sylvainbruand/FLAQ-FabLab-Air-Quality/flaq_xiao/FLAQ-3.png

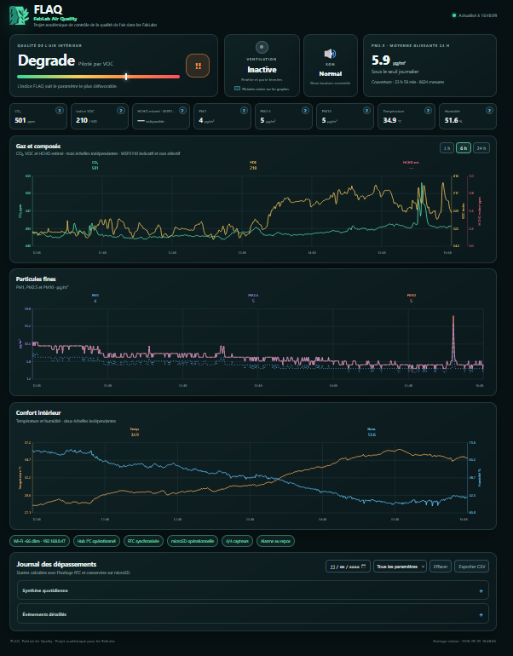
flaq_xiao/FLAQ-3.png
