sylvainbruand/FLAQ-FabLab-Air-Quality/flaq_xiao/SW/2-102010671-seeedstudio-xiao-esp32s3-plus-45font.jpg

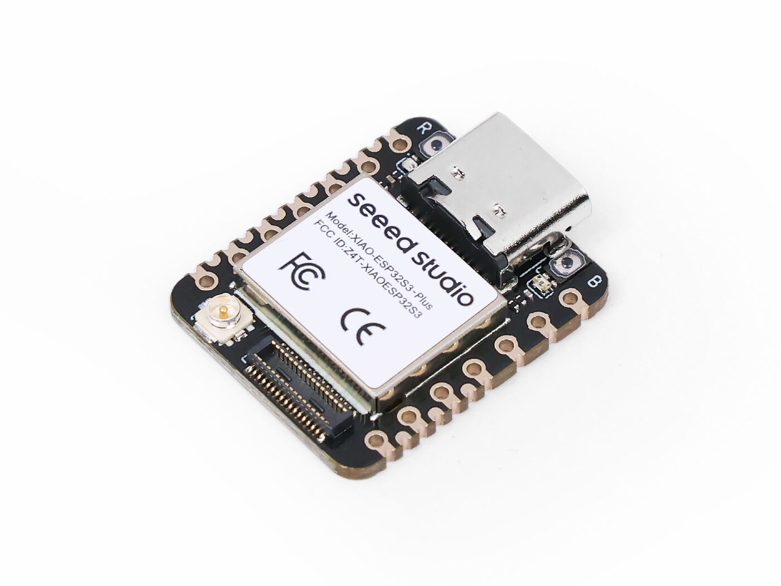
flaq_xiao/SW/2-102010671-seeedstudio-xiao-esp32s3-plus-45font.jpg
