sylvainbruand/FLAQ-FabLab-Air-Quality/flaq_xiao/SW/aeraulique-ventilation-gris.jpg

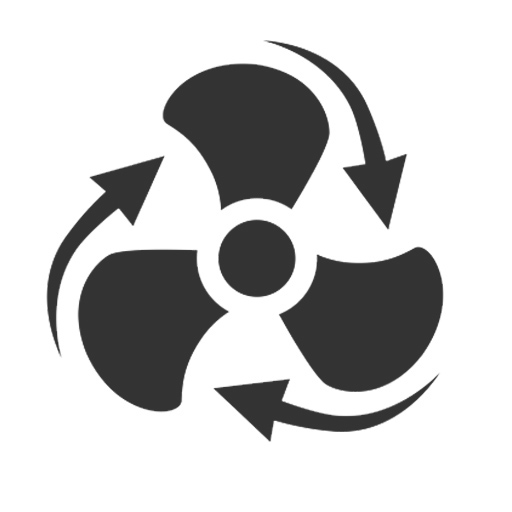
flaq_xiao/SW/aeraulique-ventilation-gris.jpg
