sylvainbruand/FLAQ-FabLab-Air-Quality/flaq_xiao/SW/modeles_3d/grove_8_ports/dessus.jpg

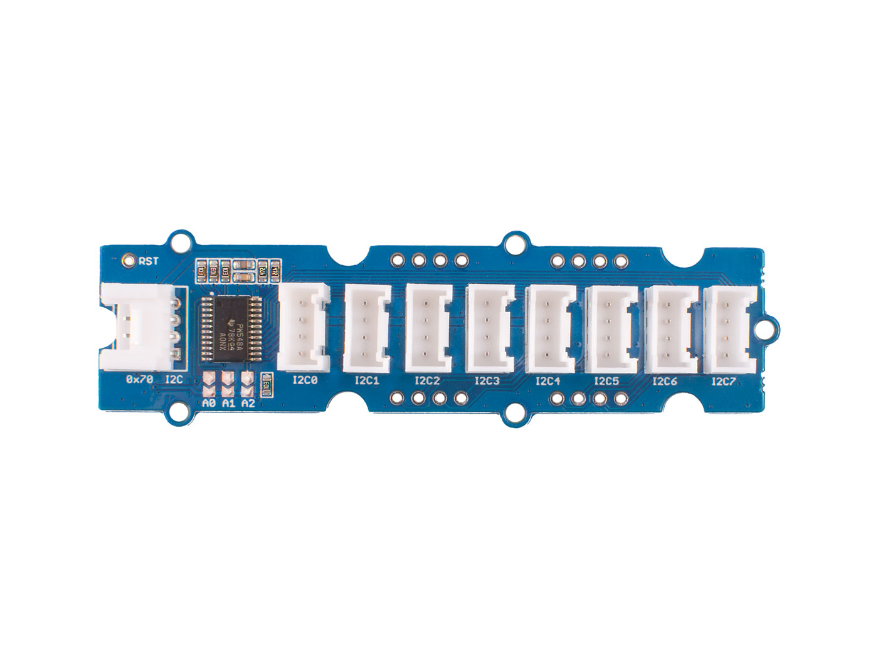
flaq_xiao/SW/modeles_3d/grove_8_ports/dessus.jpg
