sylvainbruand/FLAQ-FabLab-Air-Quality/flaq_xiao/SW/modeles_3d/scd30/apercu.bmp

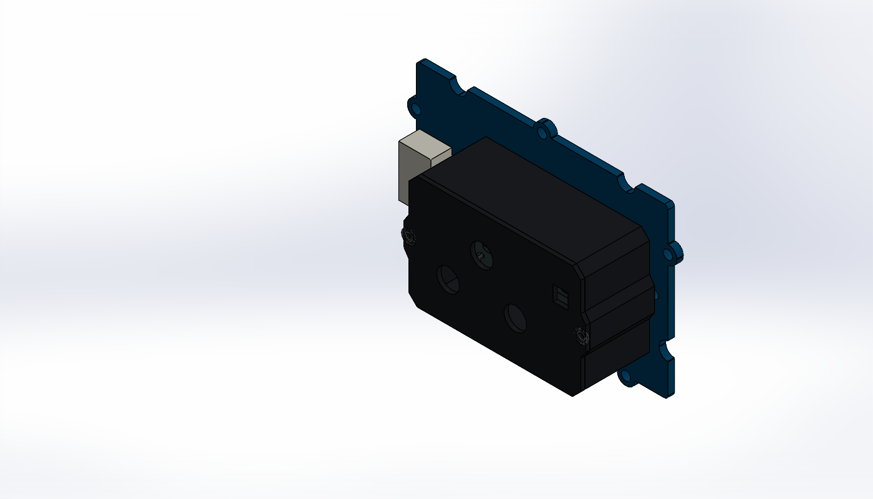
flaq_xiao/SW/modeles_3d/scd30/apercu.bmp
