sylvainbruand/FLAQ-FabLab-Air-Quality/flaq_xiao/SW/modeles_3d/scd30/import.bmp

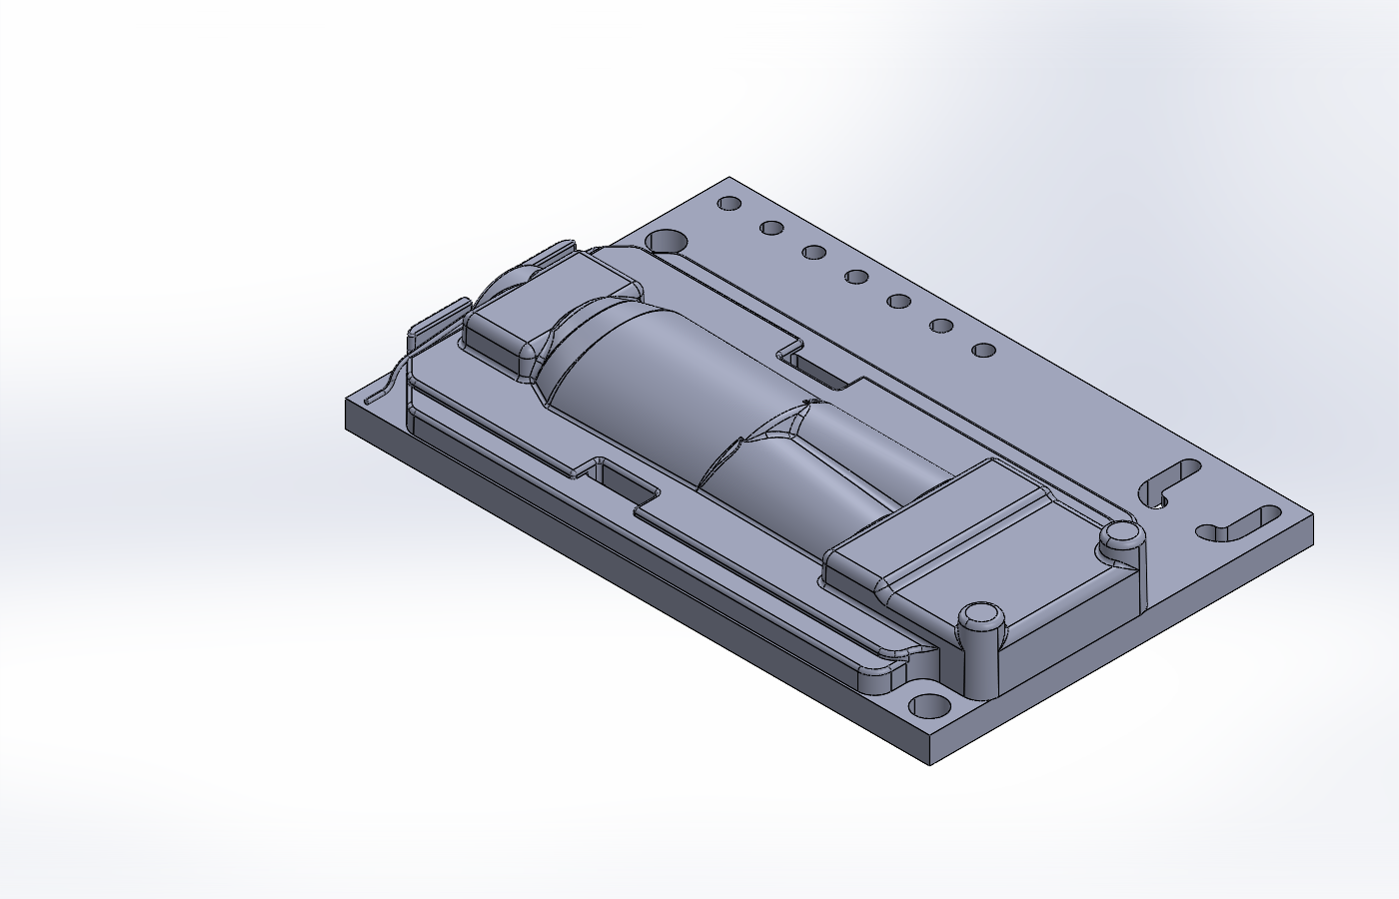
flaq_xiao/SW/modeles_3d/scd30/import.bmp
