sylvainbruand/FLAQ-FabLab-Air-Quality/flaq_xiao/SW/Screenshot 2025-02-27 170238.png

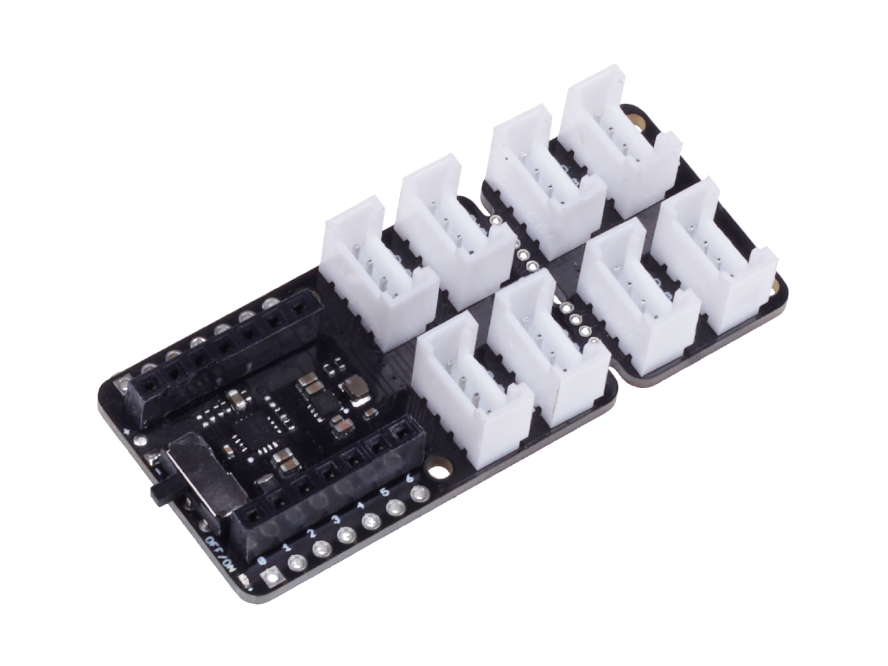
flaq_xiao/SW/Screenshot 2025-02-27 170238.png
