sylvainbruand/FLAQ-FabLab-Air-Quality/flaq_xiao/SW/OLED 128x64.SLDPRT

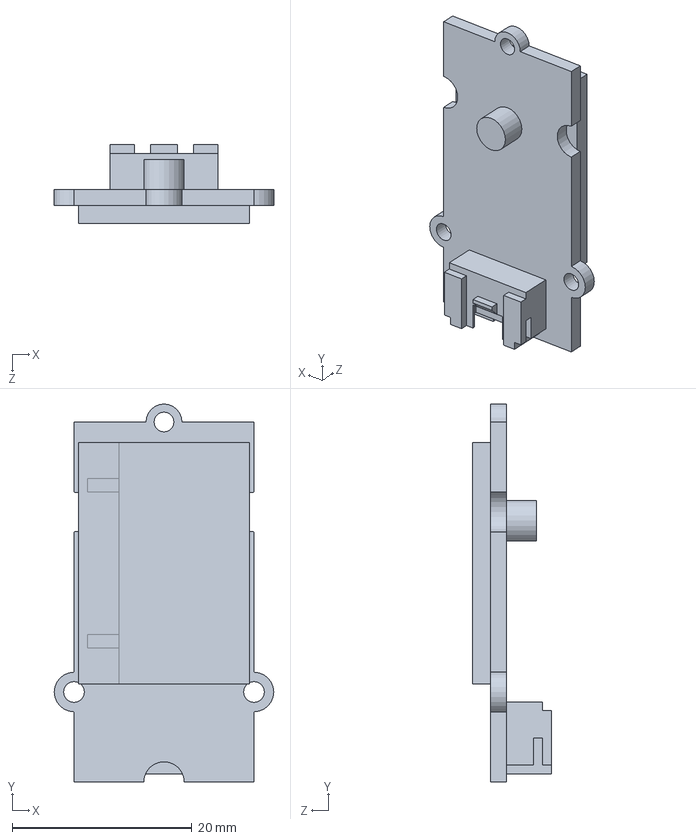
[picture p19: CAD file, 2026-09-29]
flaq_xiao/SW/OLED 128x64.SLDPRT
24.4 x 42.0 x 8.81 mm
