sylvainbruand/FLAQ-FabLab-Air-Quality/flaq_xiao/SW/Grove Shield for Seeeduino XIAO v1.step

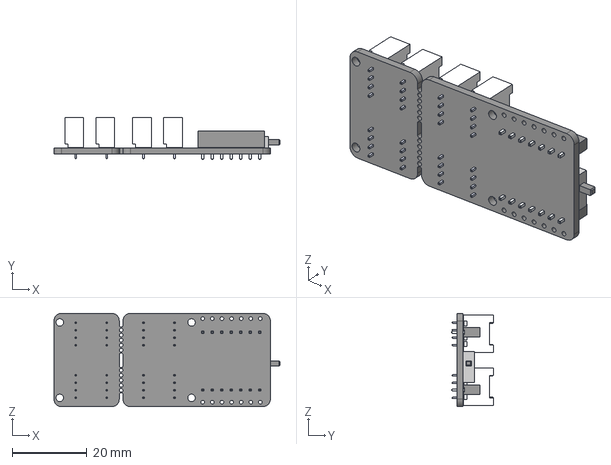
[picture p20: CAD file, 2026-09-29]
flaq_xiao/SW/Grove Shield for Seeeduino XIAO v1.step
60.4 x 11.2 x 24.9 mm
Grove Connector (standing) x 8
FemaleHeader x 2
