sylvainbruand/FLAQ-FabLab-Air-Quality/flaq_xiao/SW/buzzer.SLDPRT

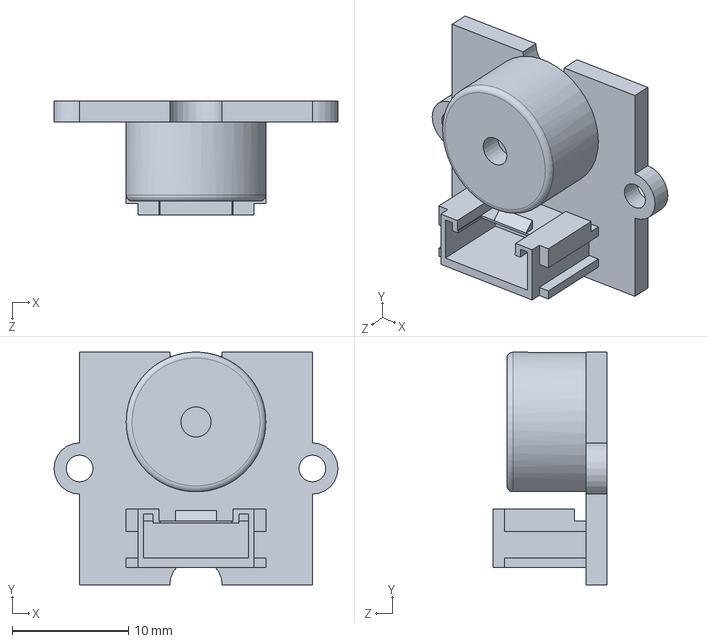
[picture p21: CAD file, 2026-09-29]
flaq_xiao/SW/buzzer.SLDPRT
24.4 x 20.0 x 9.80 mm
