sylvainbruand/FLAQ-FabLab-Air-Quality/flaq_xiao/SW/toit_xiao_V2.SLDPRT

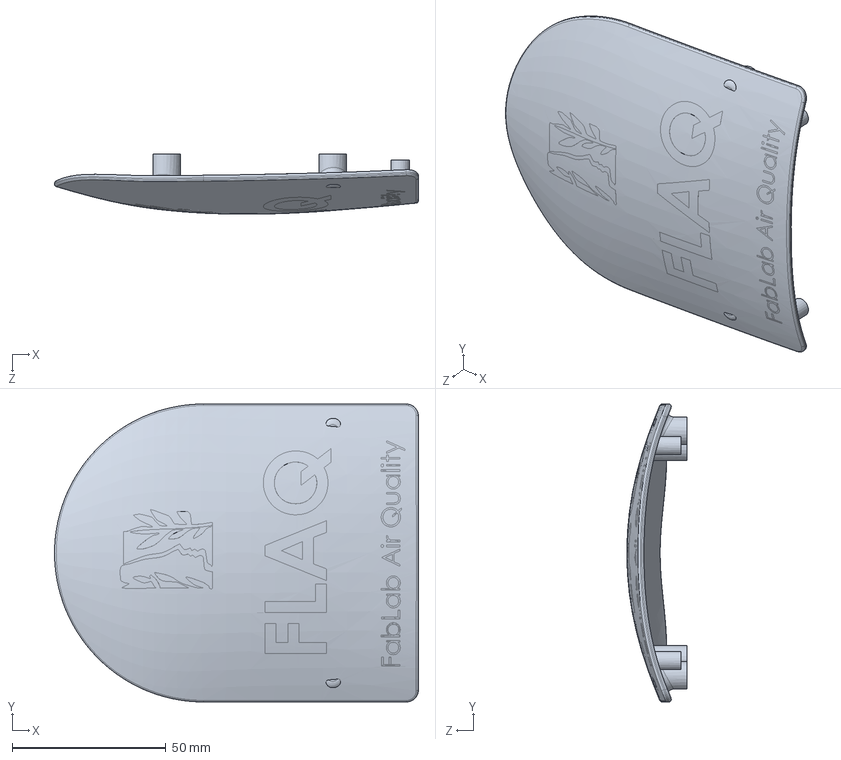
[picture p22: CAD file, 2026-09-29]
flaq_xiao/SW/toit_xiao_V2.SLDPRT
118.5 x 97.0 x 19.7 mm
