sylvainbruand/FLAQ-FabLab-Air-Quality/flaq_xiao/SW/XIAO ESP32S3 PLUS v4.step

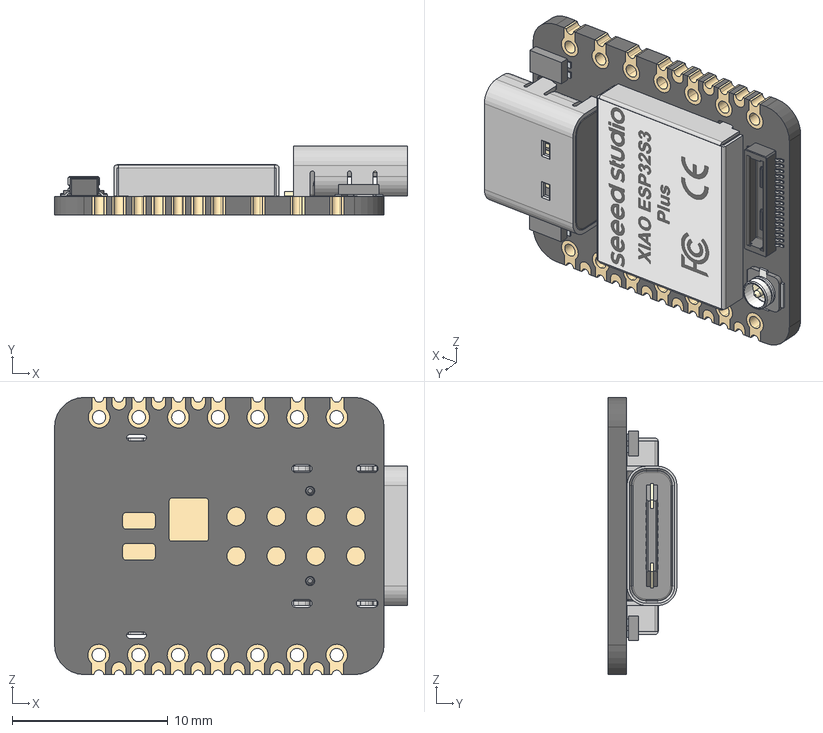
[picture p23: CAD file, 2026-09-29]
flaq_xiao/SW/XIAO ESP32S3 PLUS v4.step
22.6 x 4.42 x 17.8 mm
DF40C-30DP-0.4V_51_ v1
BOSS-EXTRUDE14_8_
BOSS-EXTRUDE7_4_
BOSS-EXTRUDE7_3_
BOSS-EXTRUDE14_4_
BOSS-EXTRUDE14_2_
BOSS-EXTRUDE14_11_
BOSS-EXTRUDE7_7_
BOSS-EXTRUDE14_9_
BOSS-EXTRUDE14_3_
BOSS-EXTRUDE14_7_
MIRROR2
BOSS-EXTRUDE14_5_
BOSS-EXTRUDE14_12_
BOSS-EXTRUDE7_8_
BOSS-EXTRUDE7_1_
BOSS-EXTRUDE14_10_
BOSS-EXTRUDE7_9_
BOSS-EXTRUDE14_6_
BOSS-EXTRUDE14_1_
BOSS-EXTRUDE7_6_
BOSS-EXTRUDE7_2_
CUT-EXTRUDE5
BOSS-EXTRUDE7_5_
Shield
Pins x 2
U.FL-R-SMT-1_10_ v1
