sylvainbruand/FLAQ-FabLab-Air-Quality/flaq_xiao/SW/T°C Humidité.SLDPRT

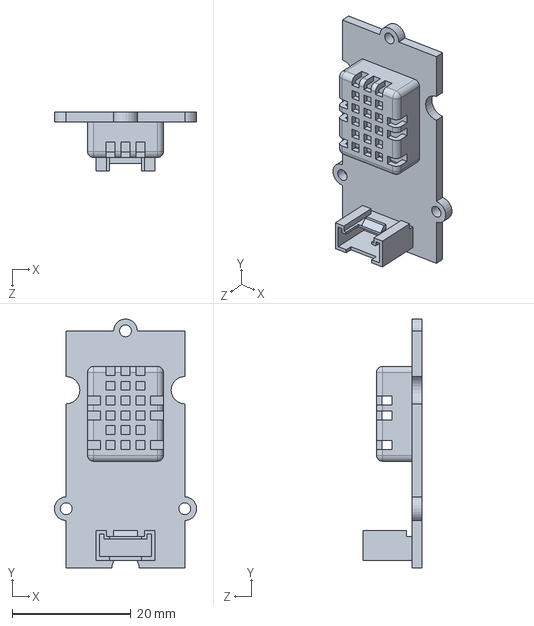
[picture p24: CAD file, 2026-09-29]
flaq_xiao/SW/T°C Humidité.SLDPRT
24.0 x 42.0 x 10.0 mm
