sylvainbruand/FLAQ-FabLab-Air-Quality/flaq_xiao/SW/couvercle_xiao-1.3mf

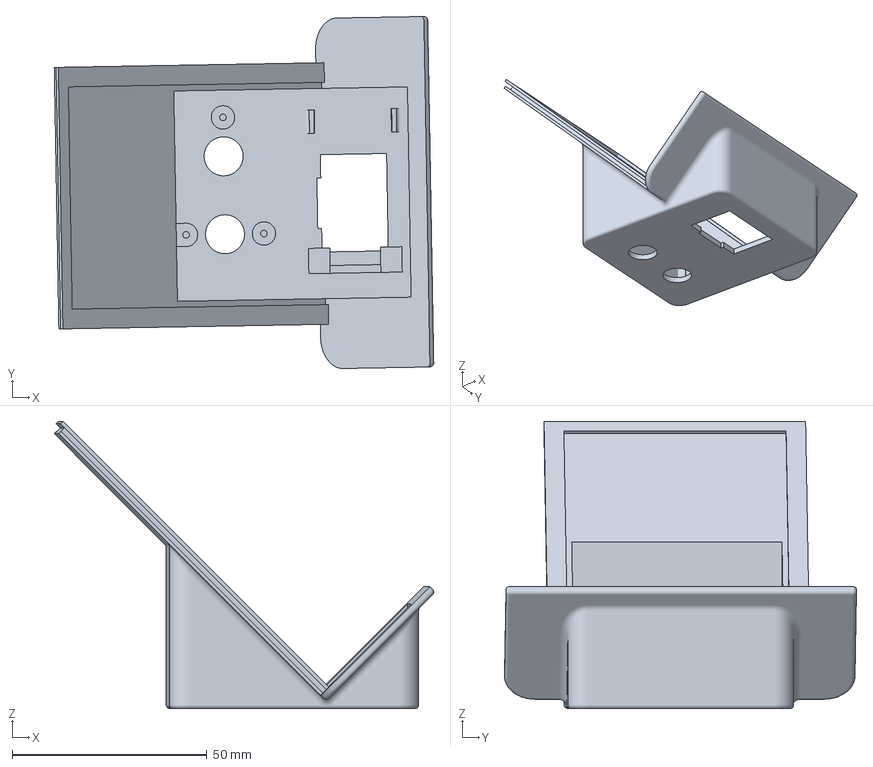
[picture p25: CAD file, 2026-09-04]
flaq_xiao/SW/couvercle_xiao-1.3mf
97.4 x 90.4 x 73.8 mm
