sylvainbruand/FLAQ-FabLab-Air-Quality/flaq_xiao/SW/couvercle_xiao.SLDPRT

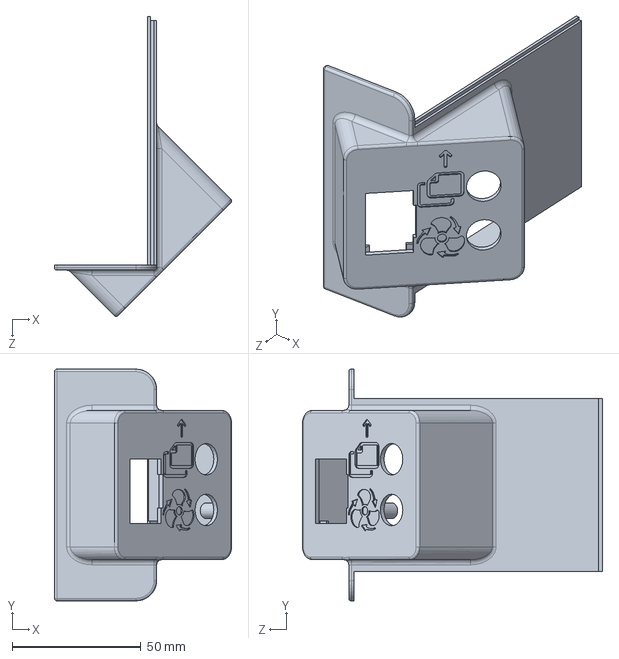
[picture p26: CAD file, 2026-09-04]
flaq_xiao/SW/couvercle_xiao.SLDPRT
68.8 x 90.0 x 116.5 mm
