sylvainbruand/FLAQ-FabLab-Air-Quality/flaq_xiao/SW/logo_BP_xiao.SLDPRT

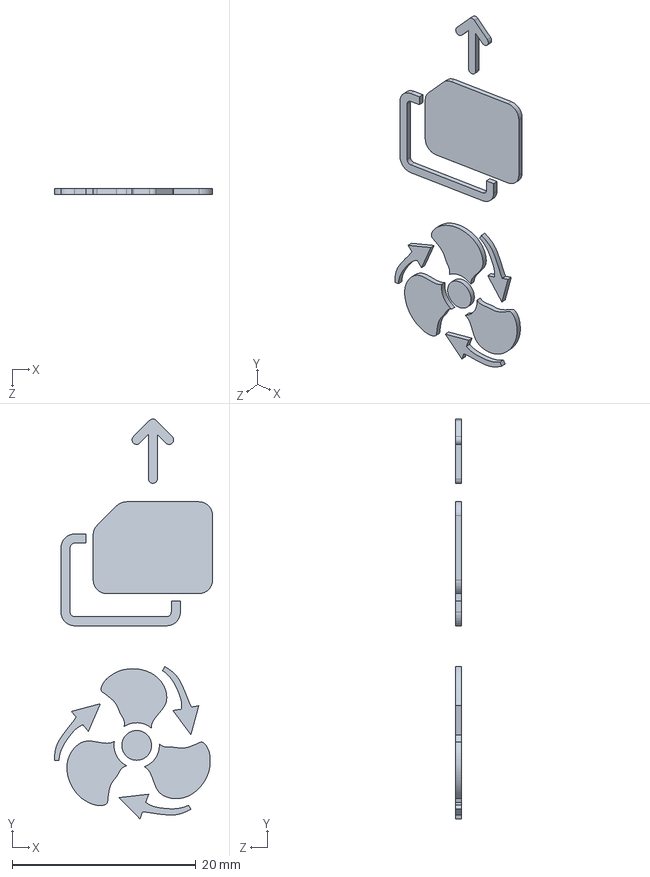
[picture p27: CAD file, 2026-09-04]
flaq_xiao/SW/logo_BP_xiao.SLDPRT
17.2 x 43.5 x 0.6 mm
