sylvainbruand/FLAQ-FabLab-Air-Quality/flaq_xiao/SW/bouchon_droite.SLDPRT

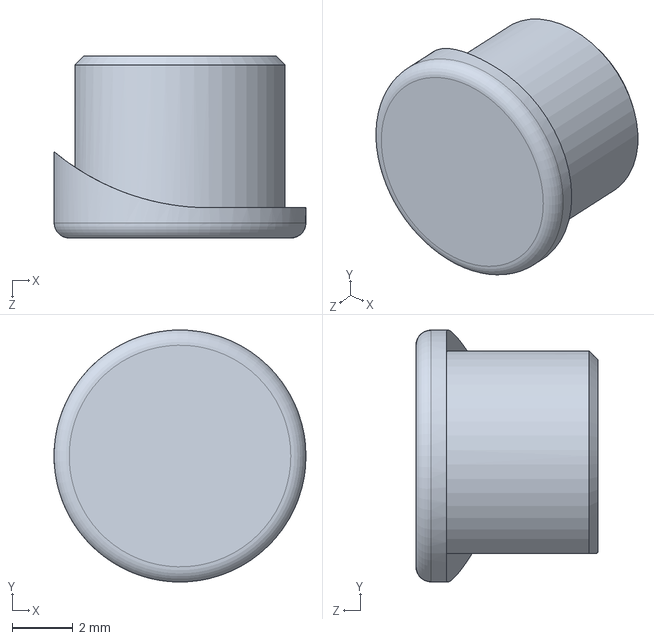
[picture p28: CAD file, 2026-08-22]
flaq_xiao/SW/bouchon_droite.SLDPRT
8.30 x 8.30 x 6.00 mm
