sylvainbruand/FLAQ-FabLab-Air-Quality/flaq_xiao/SW/bouchon2.SLDPRT

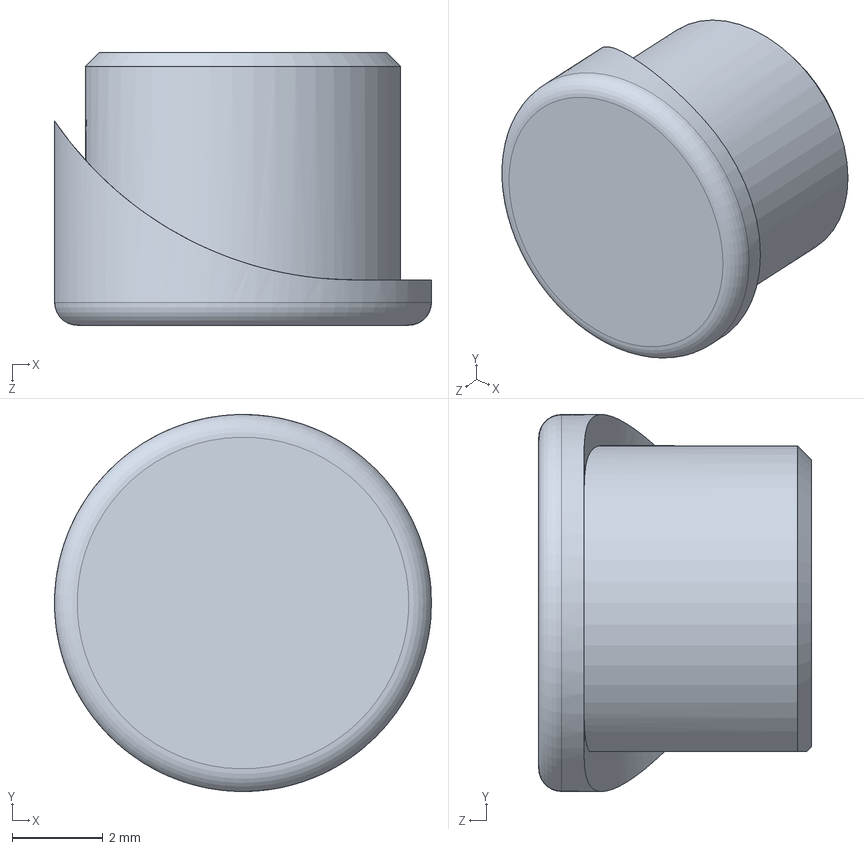
[picture p29: CAD file, 2026-08-22]
flaq_xiao/SW/bouchon2.SLDPRT
8.30 x 8.30 x 6.00 mm
