sylvainbruand/FLAQ-FabLab-Air-Quality/flaq_xiao/SW/etage stevenson.SLDPRT

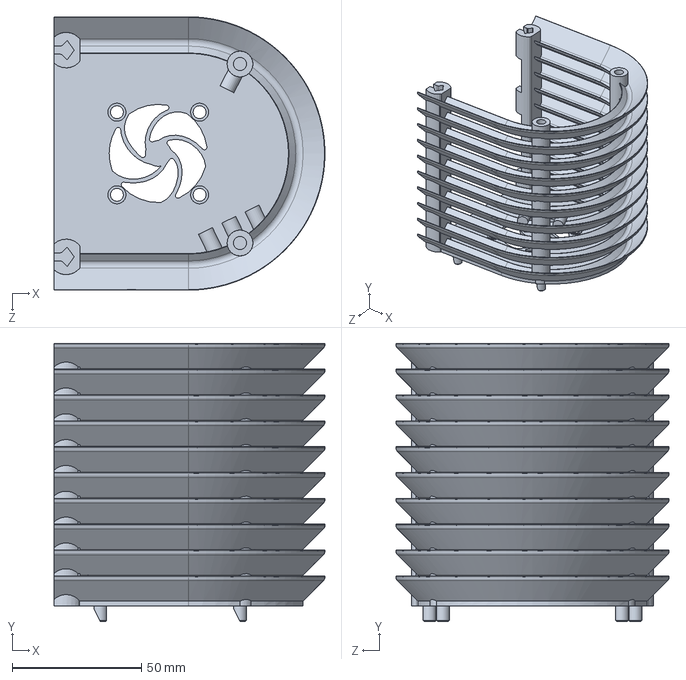
[picture p30: CAD file, 2026-08-22]
flaq_xiao/SW/etage stevenson.SLDPRT
104.9 x 107.8 x 105.8 mm
