sylvainbruand/FLAQ-FabLab-Air-Quality/flaq_xiao/SW/boitier bas.SLDPRT

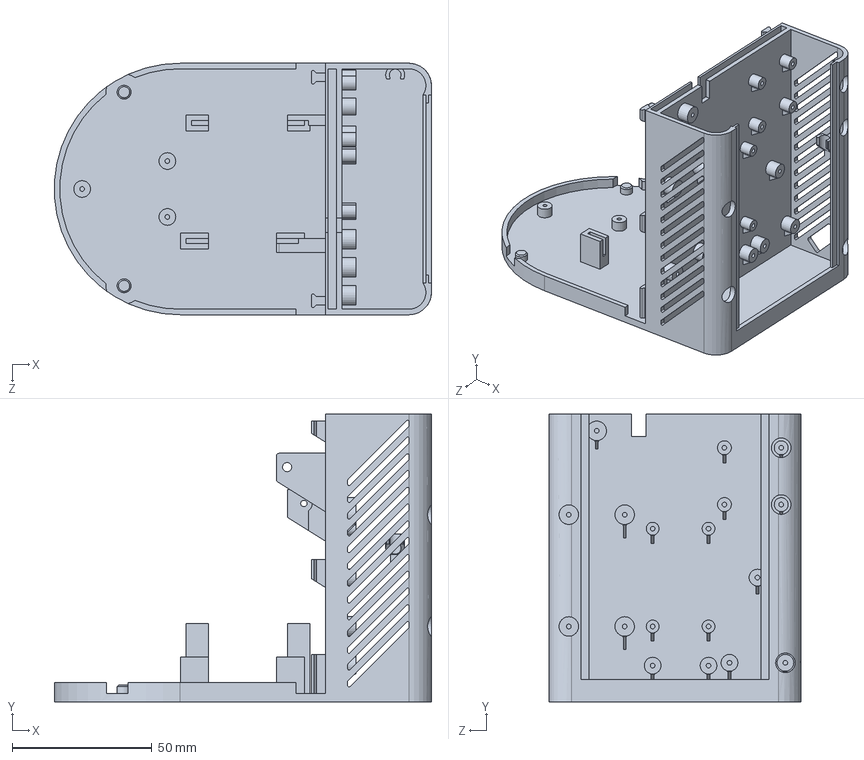
[picture p31: CAD file, 2026-08-22]
flaq_xiao/SW/boitier bas.SLDPRT
134.9 x 103.0 x 90.0 mm
