sylvainbruand/FLAQ-FabLab-Air-Quality/flaq_xiao/SW/flaq-xiao.3mf

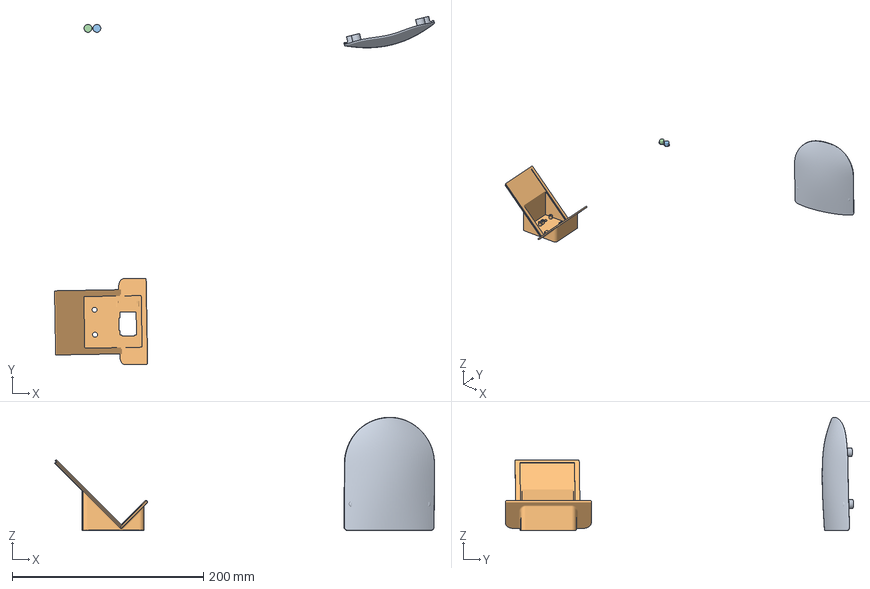
[picture p32: CAD file, 2026-08-22]
flaq_xiao/SW/flaq-xiao.3mf
397.3 x 364.3 x 118.5 mm
toit_xiao
Assemblage1^ensemble_xiao - couvercle_xiao-1
bouchon_droite.STL x 2
