sylvainbruand/FLAQ-FabLab-Air-Quality/flaq_xiao/flaq_logo.h

#pragma once

#include <Arduino.h>

const uint8_t FLAQ_LOGO_PNG[] PROGMEM = {
    0x89, 0x50, 0x4e, 0x47, 0x0d, 0x0a, 0x1a, 0x0a, 0x00, 0x00, 0x00, 0x0d,
    0x49, 0x48, 0x44, 0x52, 0x00, 0x00, 0x00, 0xc0, 0x00, 0x00, 0x00, 0xb6,
    0x08, 0x06, 0x00, 0x00, 0x00, 0x8f, 0xa7, 0x82, 0xdb, 0x00, 0x00, 0x00,
    0x01, 0x73, 0x52, 0x47, 0x42, 0x00, 0xae, 0xce, 0x1c, 0xe9, 0x00, 0x00,
    0x00, 0x04, 0x67, 0x41, 0x4d, 0x41, 0x00, 0x00, 0xb1, 0x8f, 0x0b, 0xfc,
    0x61, 0x05, 0x00, 0x00, 0x00, 0x09, 0x70, 0x48, 0x59, 0x73, 0x00, 0x00,
    0x0e, 0xc3, 0x00, 0x00, 0x0e, 0xc3, 0x01, 0xc7, 0x6f, 0xa8, 0x64, 0x00,
    0x00, 0x87, 0x91, 0x49, 0x44, 0x41, 0x54, 0x78, 0x5e, 0xed, 0xbd, 0x07,
    0x78, 0x56, 0xc7, 0x95, 0x37, 0x9e, 0x6f, 0xbf, 0x96, 0xdd, 0xec, 0x7e,
    0x9b, 0xdd, 0x6c, 0xb6, 0x17, 0x63, 0xc0, 0xc6, 0x80, 0x71, 0x2f, 0x49,
    0xdc, 0xed, 0xc4, 0x8e, 0x0b, 0x20, 0x09, 0x81, 0x3a, 0xc5, 0x14, 0x03,
    0xee, 0xf4, 0x22, 0x24, 0xd1, 0x9b, 0x40, 0xa8, 0x0b, 0x24, 0x8a, 0xc1,
    0x34, 0x21, 0xd4, 0xbb, 0x40, 0xd8, 0xd8, 0xc4, 0x76, 0x88, 0xed, 0x24,
    0x8e, 0x93, 0x0d, 0xa0, 0x57, 0x6f, 0x91, 0x5e, 0x75, 0x09, 0xb0, 0x1d,
    0x57, 0xcd, 0xff, 0x39, 0x33, 0x73, 0x66, 0xce, 0xcc, 0xbd, 0xaf, 0x10,
    0xd8, 0x9b, 0x75, 0xf2, 0xcf, 0x3c, 0xcf, 0x79, 0xee, 0x7d, 0xef, 0x9d,
    0x3b, 0x33, 0xf7, 0xbd, 0xbf, 0xdf, 0x99, 0x33, 0xed, 0xcc, 0x37, 0x22,
    0x77, 0x6f, 0x99, 0x38, 0x26, 0x3b, 0xb9, 0xf3, 0xb6, 0x9d, 0x6b, 0xbb,
    0xc7, 0xed, 0xdb, 0x96, 0xf6, 0x8d, 0xcb, 0x0c, 0x3e, 0x9f, 0xef, 0xcf,
    0x27, 0x14, 0x15, 0x84, 0x45, 0x17, 0xe5, 0xcd, 0x4a, 0x38, 0x98, 0x37,
    0x6b, 0x4a, 0xd1, 0x8e, 0x59, 0xdf, 0xdb, 0xbe, 0xf6, 0xf1, 0x5b, 0xf3,
    0x56, 0xff, 0x18, 0xce, 0xef, 0xda, 0xbe, 0xf6, 0xf1, 0x07, 0x77, 0x6e,
    0x1c, 0x17, 0xfd, 0x72, 0xd6, 0xd4, 0x87, 0x77, 0xae, 0x0f, 0xbf, 0x33,
    0x77, 0xd5, 0x23, 0xf7, 0xee, 0x58, 0xfb, 0xc8, 0x5d, 0xf9, 0x6b, 0x1e,
    0xbc, 0x6f, 0xd7, 0x86, 0x07, 0xef, 0xcb, 0x07, 0xd9, 0xfc, 0xe0, 0x23,
    0x7b, 0xd3, 0x1e, 0x7c, 0x7c, 0x6f, 0x9a, 0x38, 0xee, 0x12, 0xe7, 0x11,
    0x85, 0x99, 0x0f, 0x46, 0x14, 0xe6, 0x3e, 0x18, 0x71, 0x20, 0xf3, 0xc1,
    0x49, 0x07, 0x72, 0x1f, 0x9c, 0x54, 0x28, 0x64, 0x72, 0x61, 0xfe, 0x83,
    0xd3, 0x8a, 0x77, 0x3d, 0xf8, 0x54, 0xf9, 0xde, 0xbb, 0x4f, 0x9f, 0x3b,
    0xf7, 0xd7, 0x76, 0x99, 0xfe, 0x14, 0xfe, 0x14, 0x06, 0x1d, 0x1e, 0xdb,
    0xb9, 0xe9, 0xe9, 0x51, 0x79, 0xc9, 0xec, 0xea, 0x6d, 0x8b, 0xd8, 0x0f,
    0xb2, 0x57, 0xbe, 0x61, 0xdf, 0x1f, 0x28, 0xac, 0x7d, 0xb3, 0xfe, 0x3b,
    0xdf, 0xdf, 0xbe, 0xe1, 0xdd, 0x91, 0x3b, 0x56, 0xb3, 0x91, 0xdb, 0x57,
    0xb2, 0x51, 0x79, 0x42, 0xae, 0xcd, 0x4a, 0x64, 0xd7, 0x64, 0x25, 0xb2,
    0xd1, 0x3b, 0x56, 0xb1, 0x11, 0xd9, 0x2b, 0xd8, 0x75, 0xd9, 0x49, 0x6c,
    0x34, 0xdc, 0xcb, 0x49, 0x62, 0xd7, 0x65, 0xaf, 0x60, 0x23, 0x95, 0x24,
    0x09, 0xc9, 0x49, 0x66, 0xa3, 0x72, 0x93, 0xd9, 0x28, 0x38, 0x72, 0x49,
    0xe2, 0xbf, 0x47, 0xe7, 0xa6, 0xb0, 0xeb, 0x73, 0x93, 0xd9, 0xf5, 0x39,
    0xc9, 0xfa, 0x98, 0x9d, 0xcc, 0xc6, 0xe4, 0x80, 0xa4, 0xb0, 0x1b, 0x72,
    0x57, 0xb2, 0x3b, 0x77, 0xae, 0x6d, 0x79, 0x74, 0xef, 0xb6, 0x67, 0xec,
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
};
const size_t FLAQ_LOGO_PNG_LEN = sizeof(FLAQ_LOGO_PNG);
